DustinWatts/ESP32-S3_TFT_Combiner/Assets/img1.png

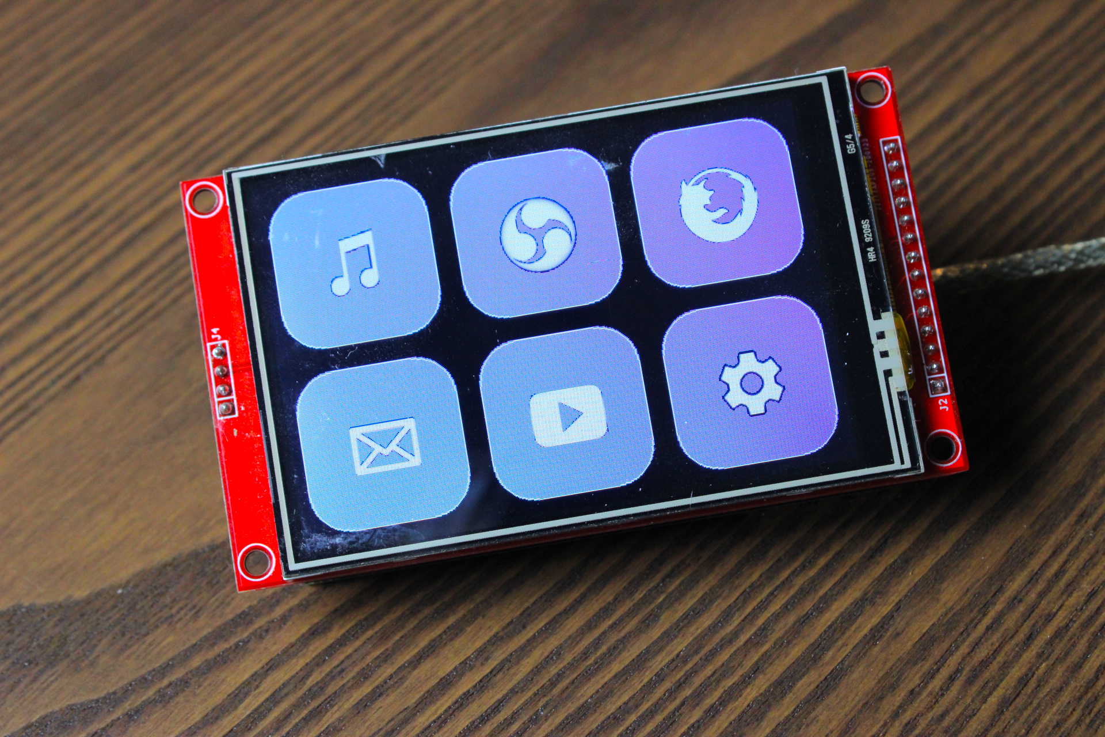
Assets/img1.png
