DustinWatts/ESP32-S3_TFT_Combiner/Assets/img3.png

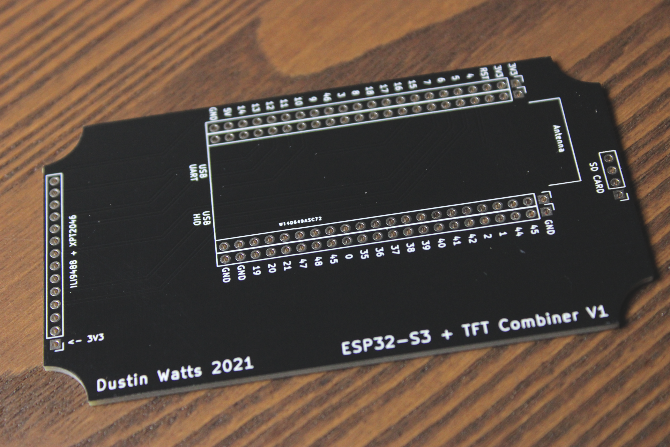
Assets/img3.png
